shapoco/lcdtap/docs/cases/espboy/thumb.jpg

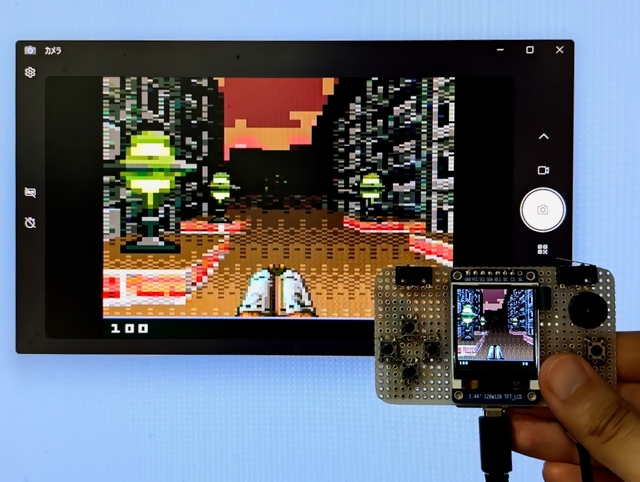
docs/cases/espboy/thumb.jpg
