shapoco/lcdtap/docs/cases/ks0108/thumb.jpg

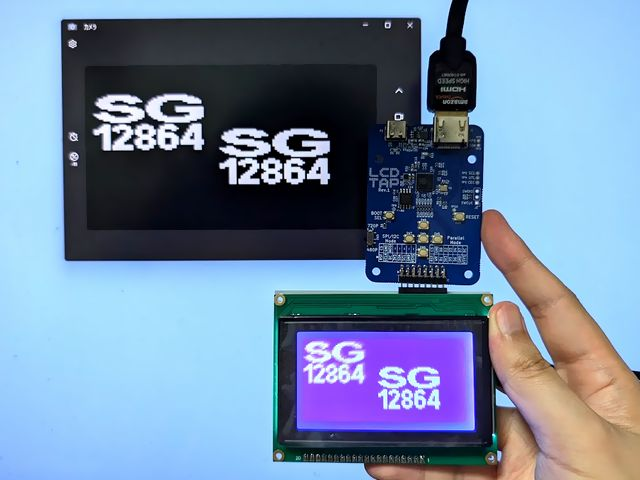
docs/cases/ks0108/thumb.jpg
