shapoco/lcdtap/docs/cases/picocalc/thumb.jpg

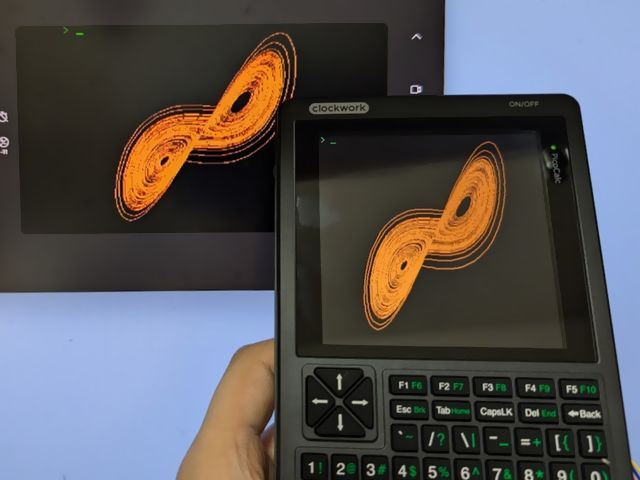
docs/cases/picocalc/thumb.jpg
