shapoco/lcdtap/docs/cases/text-display/thumb.jpg

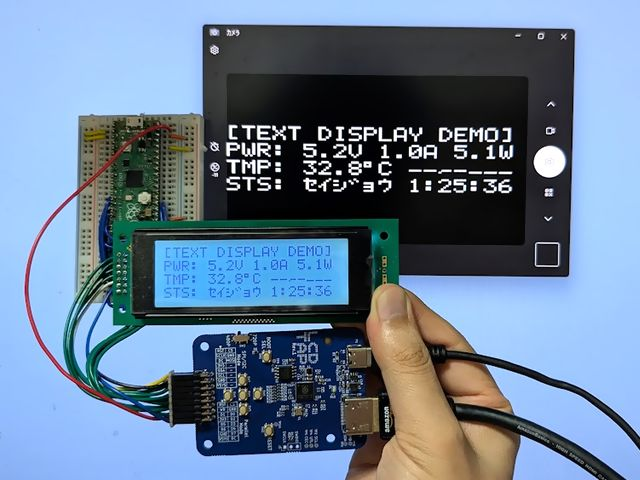
docs/cases/text-display/thumb.jpg
