shapoco/lcdtap/docs/cases/tinyjoypad/thumb.jpg

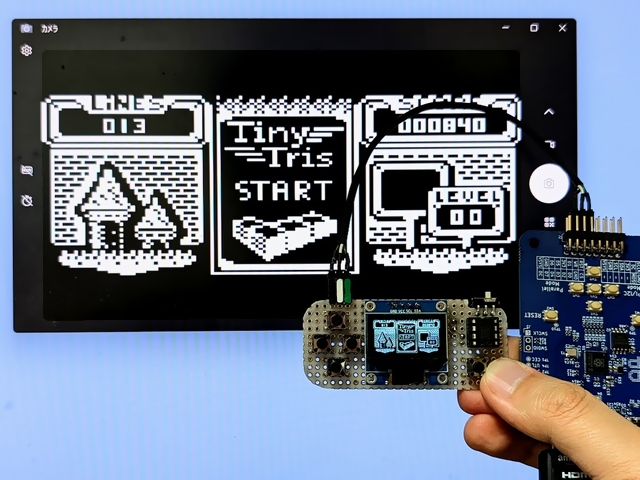
docs/cases/tinyjoypad/thumb.jpg
