shapoco/lcdtap/docs/cases/wio-terminal/thumb.jpg

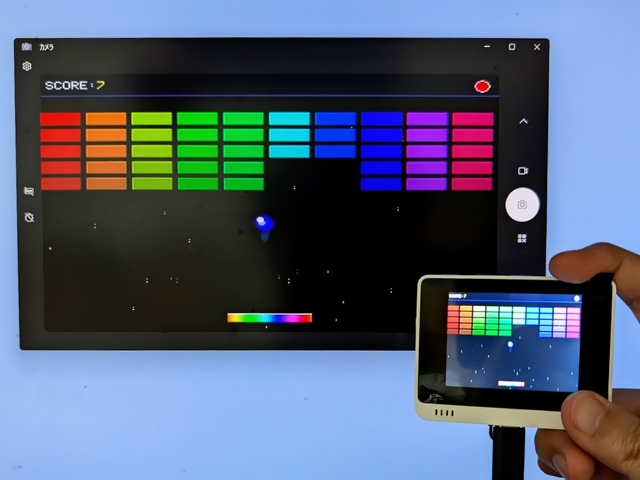
docs/cases/wio-terminal/thumb.jpg
