shapoco/lcdtap/docs/image/card.png

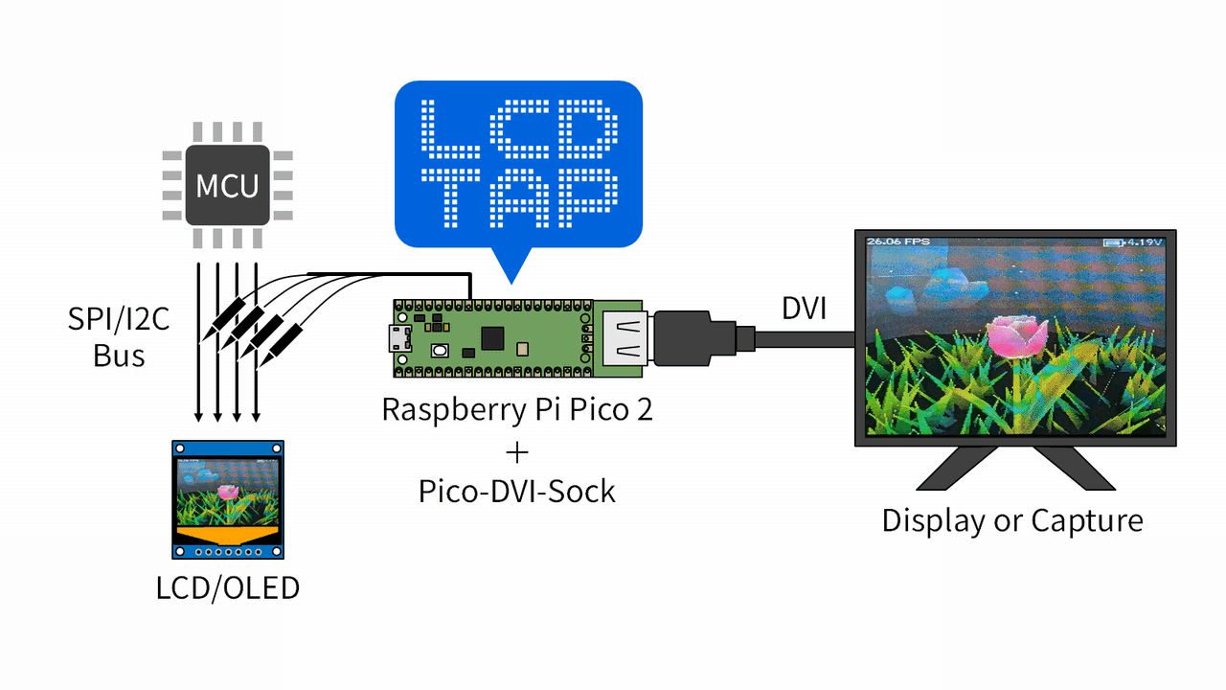
docs/image/card.png
