shapoco/lcdtap/docs/image/cover.jpg

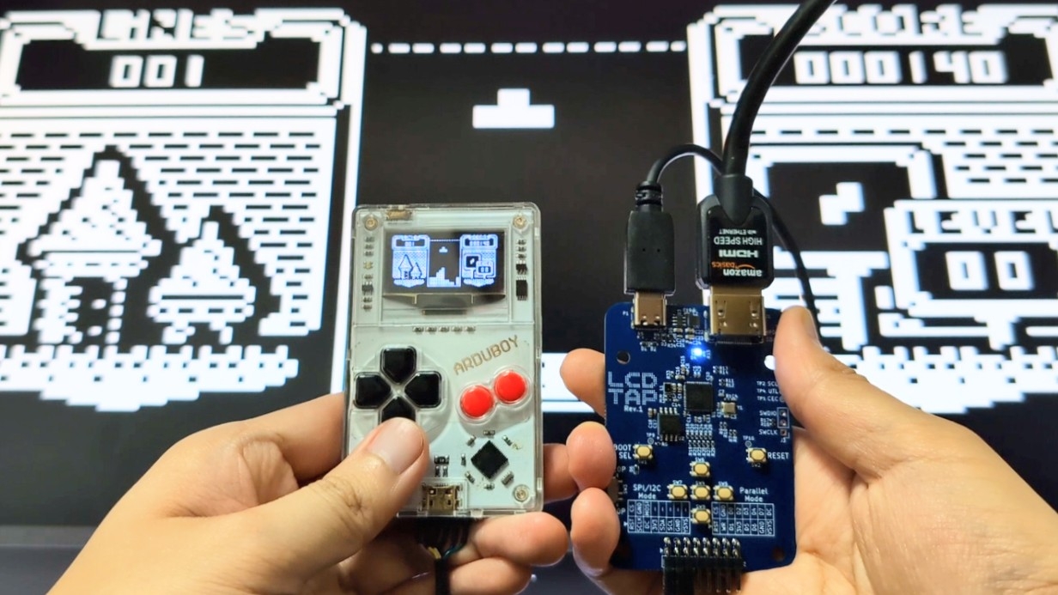
docs/image/cover.jpg
