shapoco/lcdtap/docs/image/header-and-cable.jpg

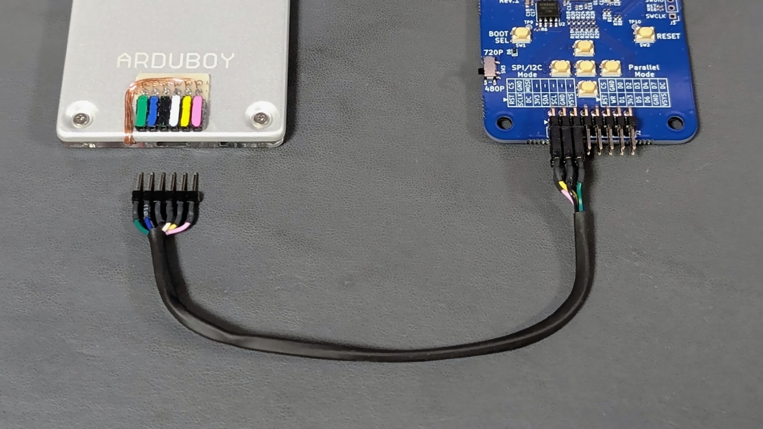
docs/image/header-and-cable.jpg
