shapoco/lcdtap/docs/image/pico2-universal-boards.jpg

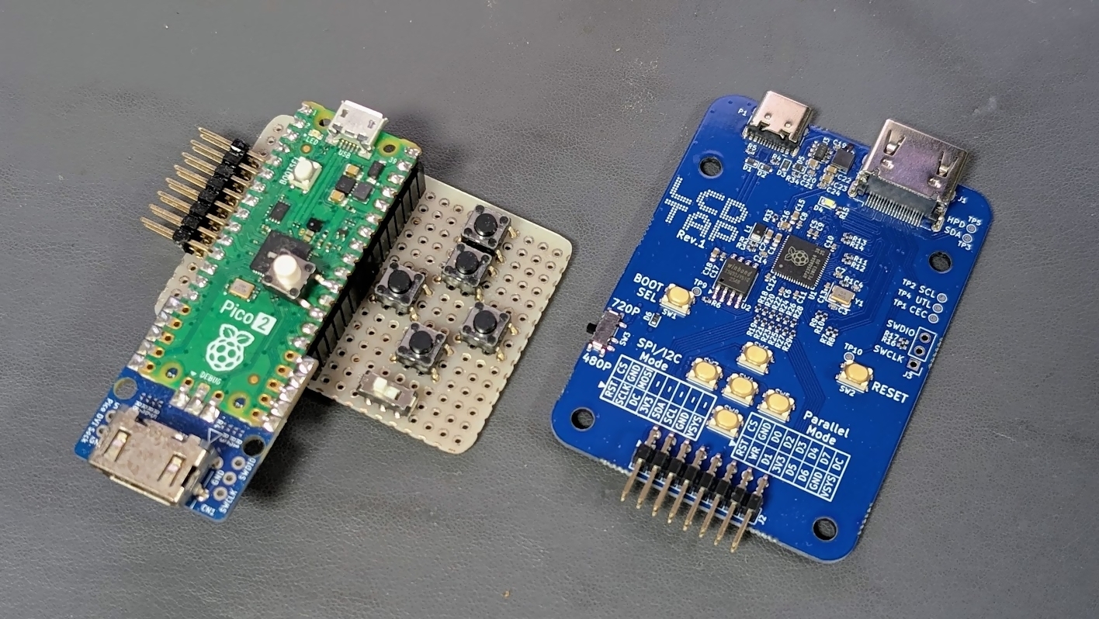
docs/image/pico2-universal-boards.jpg
