shapoco/lcdtap/docs/image/web-app.png

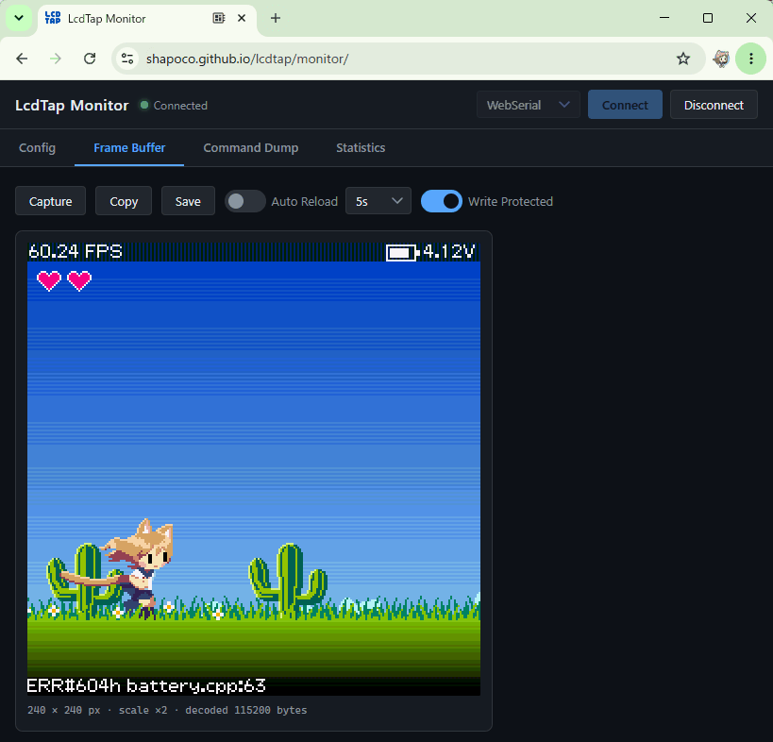
docs/image/web-app.png
