shapoco/lcdtap/docs/cases/wio-terminal/wiring.jpg

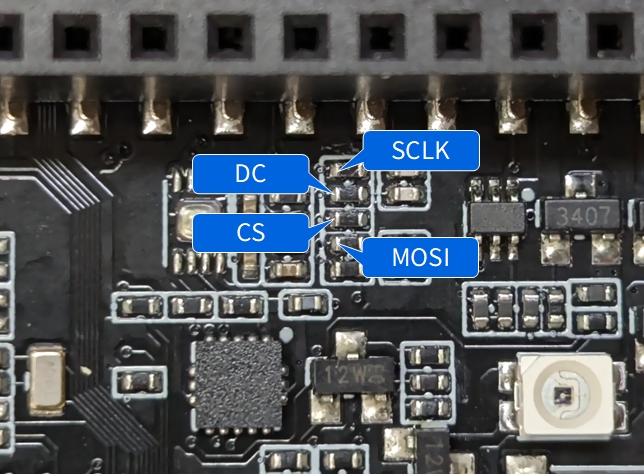
docs/cases/wio-terminal/wiring.jpg
