shapoco/lcdtap/example/pico2_common/include/lcdtap/pico2/composite_encode.hpp

#pragma once

// Composite video sample encoding. This layer has no MCU dependencies so that
// a whole field can be generated and verified on a host machine before any of
// it is run against an oscilloscope.
//
// Sample packing
// --------------
// Two DAC sinks with different transfer formats share this encoder:
//
//   R-2R : the PIO shifts right out of the OSR with an autopull threshold of
//          flushBits, so several samples are bit-packed into one 32-bit DMA
//          transfer, sample 0 in the least significant bits:
//            word = s0 | s1 << bits | s2 << (2*bits) | ...
//          Only floor(32 / bits) samples fit; the remaining high bits are
//          discarded by the autopull and never shifted out.
//   PWM  : one 16-bit counter-compare value per DMA transfer, no packing.
//
// The difference is confined to a policy chosen at init; the line structure
// below is written once. compositeEmitLine() dispatches through a function
// pointer in CompositeEncoder, so callers see no difference.
//
// Line grouping
// -------------
// samplesPerLine is not generally a multiple of samplesPerTransfer (NTSC 910,
// PAL 1135), so for the R-2R sink a single line does not occupy a whole
// number of transfers. The DMA unit is therefore a *group* of lines:
//
//   alignLines   = samplesPerTransfer / gcd(samplesPerTransfer, samplesPerLine)
//   linesPerSlot = lcm(alignLines, COMPOSITE_MIN_LINES_PER_SLOT)
//
// The PWM sink has no alignment constraint (alignLines == 1), but a group of
// one line would leave Core 1 only NUM_SLOTS-1 lines of fill budget, so the
// minimum keeps both sinks at the same safety margin.
//
// The writer runs continuously from the start of a group to its end, so no
// code below ever has to reason about alignment.

#include <cstdint>

#include "lcdtap/pico2/composite_timing.hpp"

// Hot-path placement. On the MCU the per-sample line generator must run from
// SRAM: Core 0 spins in a flash-resident loop, and a shared XIP stall on
// Core 1's fill path is enough to miss a slot deadline on PAL (see
// composite_out.cpp). The HSTX backend gets away with a flash-resident fill
// because its Core 1 only calls fillScanline -- the TMDS expansion is in
// hardware -- whereas composite also runs the whole sample encode on Core 1.
// The host test defines this to nothing so the file stays MCU-independent.
#if defined(LCDTAP_TARGET_PICO)
#include "pico.h"
#define LCDTAP_CVBS_HOT(name) __not_in_flash_func(name)
#else
#define LCDTAP_CVBS_HOT(name) name
#endif

namespace lcdtap::pico2 {

// Upper bound on linesPerSlot across all supported timing/DAC combinations
// (worst case is PAL with the R-2R DAC: gcd(4, 1135) = 1).
static constexpr uint32_t COMPOSITE_MAX_LINES_PER_SLOT = 4u;

// Floor on linesPerSlot, so that Core 1 always has at least
// (NUM_SLOTS-1) * this many lines of fill budget regardless of sink.
static constexpr uint32_t COMPOSITE_MIN_LINES_PER_SLOT = 2u;

// Colours are quantized to RGB332 before chroma encoding (LUT mode only).
static constexpr uint32_t COMPOSITE_LUT_COLORS = 256u;

// How active-video pixels are converted to chroma-modulated samples.
//
//   LUT          : RGB565 -> RGB332 index -> per-phase chroma LUT (the
//                  original path). Cheapest per pixel; colour resolution is
//                  8 bits.
//   DIRECT_NAIVE : per-pixel YUV computed with exactly the same integer math
//                  the LUT builder uses (divisions included). Bit-identical
//                  to LUT for colours representable in RGB332; full RGB565
//                  resolution otherwise. Correctness reference -- not
//                  expected to meet the PAL line budget.
//   DIRECT_OPT   : per-pixel YUV with every division folded into Q16
//                  fixed-point coefficients at init, and the subcarrier
//                  phase/sign selection hoisted out of the pixel loop (within
//                  a line, a pixel's two samples are always one U-axis and
//                  one V-axis sample with loop-invariant signs). Within +-2
//                  codes of DIRECT_NAIVE. Validated in real time on hardware
//                  for NTSC (both DACs) and PAL R-2R; PAL + PWM misses the
//                  slot deadline once the OSD overlay is drawn, so
//                  compositeOutInit() forces that combination to LUT.
enum class CompositeChromaMode : uint8_t {
  LUT = 0,
  DIRECT_NAIVE = 1,
  DIRECT_OPT = 2,
};

enum class CompositeLineType : uint8_t {
  EQ,             // equalizing pulses (two narrow sync pulses)
  SERR,           // vertical sync (two broad pulses)
  BLANK_NOBURST,  // blanked line, burst suppressed
  BLANK_BURST,    // blanked line with colour burst
  ACTIVE,         // burst plus active video
};

// Everything the line generator needs, derived once from a timing table and a
// DAC profile. Levels held here are *physical* DAC codes, so the inner loops
// never touch the normalized level space.
struct CompositeSampleWriter;
struct CompositeEncoder;

using CompositeEmitLineFn = void (*)(CompositeSampleWriter *w,
                                     const CompositeEncoder *e,
                                     CompositeLineType type, uint32_t line,
                                     const uint16_t *px);

struct CompositeEncoder {
  const CompositeTiming *timing;
  const CompositeDacProfile *dac;

  // Transfer geometry. A "transfer" is one DMA beat: a packed word for the
  // R-2R sink, a single counter-compare value for PWM.
  uint32_t samplesPerTransfer;  // 4 (R-2R 7-bit) / 1 (PWM)
  uint32_t bytesPerTransfer;    // 4 / 2
  uint32_t linesPerSlot;
  uint32_t transfersPerSlot;
  uint32_t bytesPerSlot;

  // Bit-packing parameters; used by the R-2R policy only.
  uint32_t bitsPerSample;
  uint32_t flushBits;

  // Emits one line in this sink's transfer format.
  CompositeEmitLineFn emitLine;

  // Physical DAC codes for the constant levels
  uint32_t codeSyncTip;
  uint32_t codeBlank;
  uint32_t codeWhite;
  uint32_t codeMax;

  // Burst level per subcarrier phase index (absolute sample index & 3). The
  // first index is the PAL line polarity (V switch): NTSC fills both rows with
  // the same fixed -U burst; PAL fills them with the two swinging-burst phases.
  uint32_t burstCode[2][COMPOSITE_NUM_PHASES];

  // Chroma LUT, in a sink-specific layout chosen for zero unpacking on the
  // per-pixel path:
  //
  //   R-2R: one word per colour per set.
  //     bits [13:0]  = the pixel's two 7-bit samples when it starts at `set`
  //     bits [29:16] = the same pixel when it starts at phase `set + 2`
  //   PWM : two words per colour per set, ready to store as-is.
  //     word[color]                        = s0 | s1 << 16  (starts at `set`)
  //     word[COMPOSITE_LUT_COLORS + color] = s2 | s3 << 16  (`set + 2`)
  //
  // Sets are indexed by subcarrier phase; PAL colour additionally uses the
  // upper sets for the inverted-V lines. Null in the DIRECT modes.
  uint32_t *lut;
  uint32_t lutSets;

  // Active-pixel conversion path; records which emitLine was installed.
  CompositeChromaMode chromaMode;

  // Level->code map, kept for the DIRECT_NAIVE path and the host tests (the
  // LUT path bakes it into the table at init).
  CompositeLevelMap map;

  // DIRECT_OPT constants: Q16 fixed point, pre-scaled into *physical code*
  // space so the pixel loop is multiply/add/shift only:
  //
  //   code(sample) = clamp((dirBaseQ16 + y*dirKyQ16 +- d*dirK{u,v}Q16) >> 16)
  //
  // where d is (B-Y) or (R-Y). dirBaseQ16 carries lvlBlack plus the +0.5
  // rounding of the final shift; dirKuQ16/dirKvQ16 fold the 0.492/0.879
  // demodulation constants, lumaSpan, chromaGain and the level->code scale
  // into a single coefficient. Divisions happen once here, never per pixel.
  int32_t dirBaseQ16;
  int32_t dirKyQ16;
  int32_t dirKuQ16;
  int32_t dirKvQ16;
};

// Sequential sample writer. `sampleIndex` counts absolute samples and drives
// subcarrier phase, so nothing needs to be transfer-aligned. This struct is
// only the boundary state between lines: the emit functions load it into
// locals on entry and store it back on exit, because going through a pointer
// inside the sample loops forces the compiler to reload every member after
// each buffer store (the stores and the members are both uint32_t, so it must
// assume they alias). acc/nbits are used by the R-2R bit packer only.
struct CompositeSampleWriter {
  union {
    uint32_t *w;  // R-2R: packed words
    uint16_t *h;  // PWM: one counter-compare value per sample
  } dst;
  uint32_t acc;
  uint32_t nbits;
  uint32_t sampleIndex;
};

// Compute the derived geometry, the physical level codes and (in LUT mode)
// the chroma LUT. `lutStorage` must hold at least compositeLutWords() uint32_t
// in LUT mode; the DIRECT modes ignore it and accept nullptr.
// Returns false if the combination is unsupported.
bool compositeEncoderInit(
    CompositeEncoder *e, const CompositeTiming *timing,
    const CompositeDacProfile *dac, uint32_t *lutStorage,
    CompositeChromaMode chromaMode = CompositeChromaMode::LUT);

// Number of uint32_t the caller must provide for the LUT. Depends on the DAC:
// the PWM layout stores two words per colour (see CompositeEncoder::lut).
// Zero in the DIRECT modes, which use no LUT.
uint32_t compositeLutWords(
    const CompositeTiming *timing, const CompositeDacProfile *dac,
    CompositeChromaMode chromaMode = CompositeChromaMode::LUT);

// Geometry of one line group, for the given timing and DAC profile.
uint32_t compositeLinesPerSlot(const CompositeTiming *timing,
                               const CompositeDacProfile *dac);
uint32_t compositeTransfersPerSlot(const CompositeTiming *timing,
                                   const CompositeDacProfile *dac);
uint32_t compositeBytesPerSlot(const CompositeTiming *timing,
                               const CompositeDacProfile *dac);

// Normalized 7-bit level -> physical DAC code. Init-time only.
uint32_t compositeLevelToCode(const CompositeLevelMap &map, int32_t level);

// RGB565 -> RGB888 by MSB replication. Shared by the DIRECT paths and the
// host tests so both sides agree on the expansion bit for bit.
inline void compositeRgb565To888(uint32_t v, int32_t *r8, int32_t *g8,
                                 int32_t *b8) {
  *r8 = static_cast<int32_t>(((v >> 8) & 0xF8u) | (v >> 13));
  *g8 = static_cast<int32_t>(((v >> 3) & 0xFCu) | ((v >> 9) & 0x03u));
  *b8 = static_cast<int32_t>(((v << 3) & 0xF8u) | ((v >> 2) & 0x07u));
}

// One luma+chroma sample for an RGB888 colour at absolute sample index
// `phase` (only the low two bits matter), with the PAL V-switch sign vSign
// (+1 normal line, -1 inverted line). Returns a physical DAC code. This is
// the single source of truth for the chroma math: the LUT builder, the
// DIRECT_NAIVE hot path and the host tests all evaluate exactly this
// function, which is what makes "LUT vs direct" verifiable bit for bit.
// Out-of-line wrapper for init/test use; the hot paths inline it.
uint32_t compositeChromaSampleAt(const CompositeTiming *timing,
                                 const CompositeLevelMap &map, int32_t r8,
                                 int32_t g8, int32_t b8, uint32_t phase,
                                 int32_t vSign);

// Classify a field line and, for active lines, report the source row.
CompositeLineType compositeClassifyLine(const CompositeTiming *timing,
                                        uint32_t line, uint32_t *activeY);

// Seeds the writer for the slot whose first line is `firstLine`. The subcarrier
// phase is taken from sampleIndex & 3, so sampleIndex must start at the slot's
// absolute sample offset -- not zero -- or the phase resets every slot. It
// happens to land on 0 for NTSC and PAL R-2R, but PAL PWM (linesPerSlot 2,
// 2*1135 == 2 mod 4) would flip 180 degrees on alternate slots.
void compositeWriterInit(CompositeSampleWriter *w, const CompositeEncoder *e,
                         void *dst, uint32_t firstLine);

// Emit exactly timing->samplesPerLine samples for one line, in the transfer
// format of the sink the encoder was initialized for. `line` is the absolute
// field line, used for the PAL V switch (line polarity). `px` is ignored for
// every type except ACTIVE, where it must hold hActivePixels RGB565 values.
inline void compositeEmitLine(CompositeSampleWriter *w,
                              const CompositeEncoder *e, CompositeLineType type,
                              uint32_t line, const uint16_t *px) {
  e->emitLine(w, e, type, line, px);
}

// The concrete formats: one per sink x chroma mode. Callers should use
// compositeEmitLine() instead; these are what compositeEncoderInit()
// installs according to the DAC kind and CompositeChromaMode.
void compositeEmitLinePacked(CompositeSampleWriter *w,
                             const CompositeEncoder *e, CompositeLineType type,
                             uint32_t line, const uint16_t *px);
void compositeEmitLinePackedNaive(CompositeSampleWriter *w,
                                  const CompositeEncoder *e,
                                  CompositeLineType type, uint32_t line,
                                  const uint16_t *px);
void compositeEmitLinePackedOpt(CompositeSampleWriter *w,
                                const CompositeEncoder *e,
                                CompositeLineType type, uint32_t line,
                                const uint16_t *px);
void compositeEmitLinePwm(CompositeSampleWriter *w, const CompositeEncoder *e,
                          CompositeLineType type, uint32_t line,
                          const uint16_t *px);
void compositeEmitLinePwmNaive(CompositeSampleWriter *w,
                               const CompositeEncoder *e,
                               CompositeLineType type, uint32_t line,
                               const uint16_t *px);
void compositeEmitLinePwmOpt(CompositeSampleWriter *w,
                             const CompositeEncoder *e, CompositeLineType type,
                             uint32_t line, const uint16_t *px);
// Variant without the runtime codeMax clamp, installed by
// compositeEncoderInit() only after it has proven -- exhaustively, over every
// RGB565 colour -- that no sample can exceed codeMax with the current timing
// constants. Output-identical to compositeEmitLinePwmOpt by construction.
void compositeEmitLinePwmOptNoClamp(CompositeSampleWriter *w,
                                    const CompositeEncoder *e,
                                    CompositeLineType type, uint32_t line,
                                    const uint16_t *px);

}  // namespace lcdtap::pico2
