shapoco/lcdtap/example/pico2_universal/include/splash.hpp

#ifndef LCDTAP_PICO2_UNIVERSAL_SPLASH_HPP
#define LCDTAP_PICO2_UNIVERSAL_SPLASH_HPP

#include <stdint.h>

namespace lcdtap::pico2 {

// 75x60px, RGB565
// B:G:R, Big Endian, Horizontal Adressing
// 9000 Bytes
const uint8_t splashImage[] = {
    0x25, 0xdf, 0x25, 0xdf, 0x00, 0x00, 0x25, 0xdf, 0x25, 0xdf, 0x00, 0x00,
    0x00, 0x00, 0x00, 0x00, 0x00, 0x00, 0x00, 0x00, 0x00, 0x00, 0x00, 0x00,
    0x00, 0x00, 0x00, 0x00, 0x00, 0x00, 0x00, 0x00, 0x00, 0x00, 0x00, 0x00,
    0x00, 0x00, 0x00, 0x00, 0x00, 0x00, 0x00, 0x00, 0x00, 0x00, 0x00, 0x00,
    0x00, 0x00, 0x00, 0x00, 0x00, 0x00, 0x00, 0x00, 0x00, 0x00, 0x00, 0x00,
    0x00, 0x00, 0x00, 0x00, 0x25, 0xdf, 0x25, 0xdf, 0x00, 0x00, 0x25, 0xdf,
    0x25, 0xdf, 0x00, 0x00, 0x25, 0xdf, 0x25, 0xdf, 0x00, 0x00, 0x25, 0xdf,
    0x25, 0xdf, 0x00, 0x00, 0x25, 0xdf, 0x25, 0xdf, 0x00, 0x00, 0x25, 0xdf,
    0x25, 0xdf, 0x00, 0x00, 0x00, 0x00, 0x00, 0x00, 0x25, 0xdf, 0x25, 0xdf,
    0x00, 0x00, 0x25, 0xdf, 0x25, 0xdf, 0x00, 0x00, 0x25, 0xdf, 0x25, 0xdf,
    0x00, 0x00, 0x25, 0xdf, 0x25, 0xdf, 0x00, 0x00, 0x25, 0xdf, 0x25, 0xdf,
    0x00, 0x00, 0x25, 0xdf, 0x25, 0xdf, 0x00, 0x00, 0x00, 0x00, 0x00, 0x00,
    0x00, 0x00, 0x00, 0x00, 0x00, 0x00, 0x25, 0xdf, 0x25, 0xdf, 0x00, 0x00,
    0x25, 0xdf, 0x25, 0xdf, 0x00, 0x00, 0x00, 0x00, 0x00, 0x00, 0x00, 0x00,
    0x00, 0x00, 0x00, 0x00, 0x00, 0x00, 0x00, 0x00, 0x00, 0x00, 0x00, 0x00,
    0x00, 0x00, 0x00, 0x00, 0x00, 0x00, 0x00, 0x00, 0x00, 0x00, 0x00, 0x00,
    0x00, 0x00, 0x00, 0x00, 0x00, 0x00, 0x00, 0x00, 0x00, 0x00, 0x00, 0x00,
    0x00, 0x00, 0x00, 0x00, 0x00, 0x00, 0x00, 0x00, 0x00, 0x00, 0x25, 0xdf,
    0x25, 0xdf, 0x00, 0x00, 0x25, 0xdf, 0x25, 0xdf, 0x00, 0x00, 0x25, 0xdf,
    0x25, 0xdf, 0x00, 0x00, 0x25, 0xdf, 0x25, 0xdf, 0x00, 0x00, 0x25, 0xdf,
    0x25, 0xdf, 0x00, 0x00, 0x25, 0xdf, 0x25, 0xdf, 0x00, 0x00, 0x00, 0x00,
    0x00, 0x00, 0x25, 0xdf, 0x25, 0xdf, 0x00, 0x00, 0x25, 0xdf, 0x25, 0xdf,
    0x00, 0x00, 0x25, 0xdf, 0x25, 0xdf, 0x00, 0x00, 0x25, 0xdf, 0x25, 0xdf,
    0x00, 0x00, 0x25, 0xdf, 0x25, 0xdf, 0x00, 0x00, 0x25, 0xdf, 0x25, 0xdf,
    0x00, 0x00, 0x00, 0x00, 0x00, 0x00, 0x00, 0x00, 0x00, 0x00, 0x00, 0x00,
    0x00, 0x00, 0x00, 0x00, 0x00, 0x00, 0x00, 0x00, 0x00, 0x00, 0x00, 0x00,
    0x00, 0x00, 0x00, 0x00, 0x00, 0x00, 0x00, 0x00, 0x00, 0x00, 0x00, 0x00,
    0x00, 0x00, 0x00, 0x00, 0x00, 0x00, 0x00, 0x00, 0x00, 0x00, 0x00, 0x00,
    0x00, 0x00, 0x00, 0x00, 0x00, 0x00, 0x00, 0x00, 0x00, 0x00, 0x00, 0x00,
    0x00, 0x00, 0x00, 0x00, 0x00, 0x00, 0x00, 0x00, 0x00, 0x00, 0x00, 0x00,
    0x00, 0x00, 0x00, 0x00, 0x00, 0x00, 0x00, 0x00, 0x00, 0x00, 0x00, 0x00,
    0x00, 0x00, 0x00, 0x00, 0x00, 0x00, 0x00, 0x00, 0x00, 0x00, 0x00, 0x00,
    0x00, 0x00, 0x00, 0x00, 0x00, 0x00, 0x00, 0x00, 0x00, 0x00, 0x00, 0x00,
    0x00, 0x00, 0x00, 0x00, 0x00, 0x00, 0x00, 0x00, 0x00, 0x00, 0x00, 0x00,
    0x00, 0x00, 0x00, 0x00, 0x00, 0x00, 0x00, 0x00, 0x00, 0x00, 0x00, 0x00,
    0x00, 0x00, 0x00, 0x00, 0x00, 0x00, 0x00, 0x00, 0x00, 0x00, 0x00, 0x00,
    0x00, 0x00, 0x00, 0x00, 0x00, 0x00, 0x00, 0x00, 0x00, 0x00, 0x00, 0x00,
    0x00, 0x00, 0x00, 0x00, 0x00, 0x00, 0x25, 0xdf, 0x25, 0xdf, 0x00, 0x00,
    0x25, 0xdf, 0x25, 0xdf, 0x00, 0x00, 0x00, 0x00, 0x00, 0x00, 0x00, 0x00,
    0x00, 0x00, 0x00, 0x00, 0x00, 0x00, 0x00, 0x00, 0x00, 0x00, 0x00, 0x00,
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
};

constexpr uint16_t SPLASH_WIDTH = 75;
constexpr uint16_t SPLASH_HEIGHT = 60;

}  // namespace lcdtap::pico2

#endif
